ttnnijmegen/plantsensor/pcb/pdf/higrow1_etch_silk_bottom.pdf

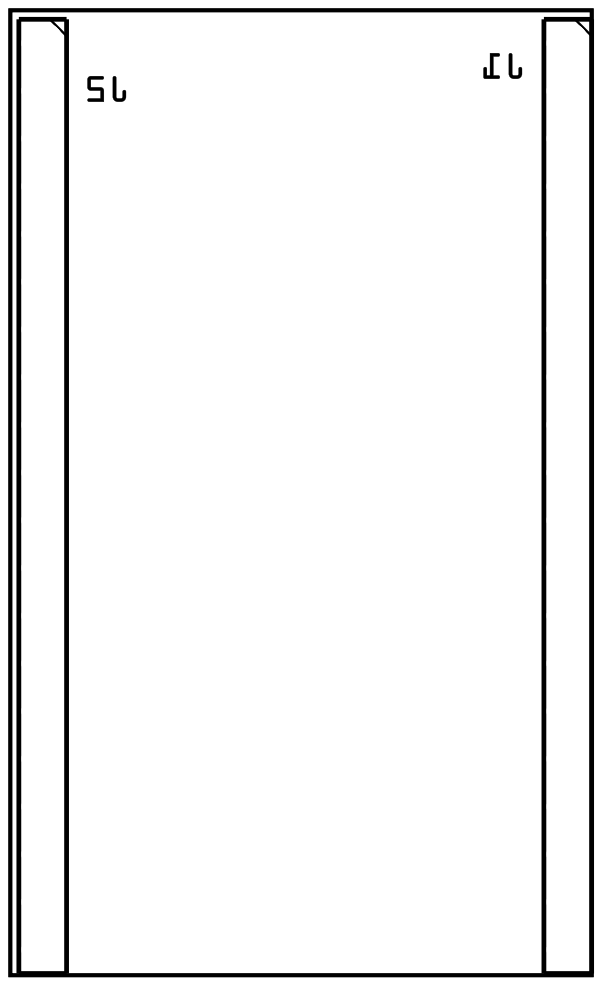
[picture p71: page 1]
