ttnnijmegen/plantsensor/pcb/pdf/higrow1_etch_silk_bottom_mirror.pdf

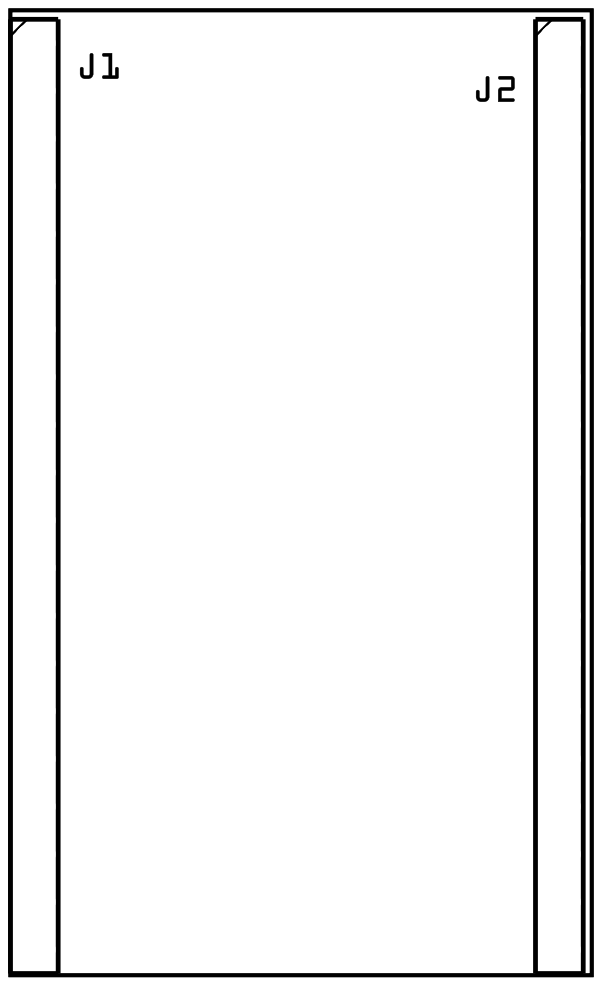
[picture p72: page 1]
