ttnnijmegen/plantsensor/pcb/pdf/higrow1_etch_silk_top.pdf

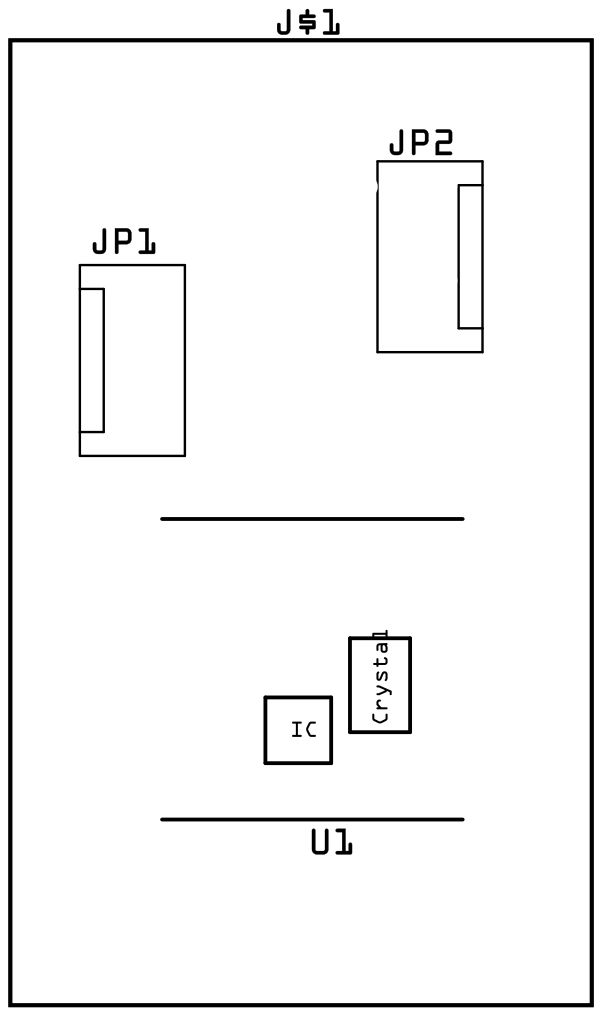
[picture p73: page 1]
