ttnnijmegen/plantsensor/pcb/pdf/higrow1_etch_silk_top_mirror.pdf

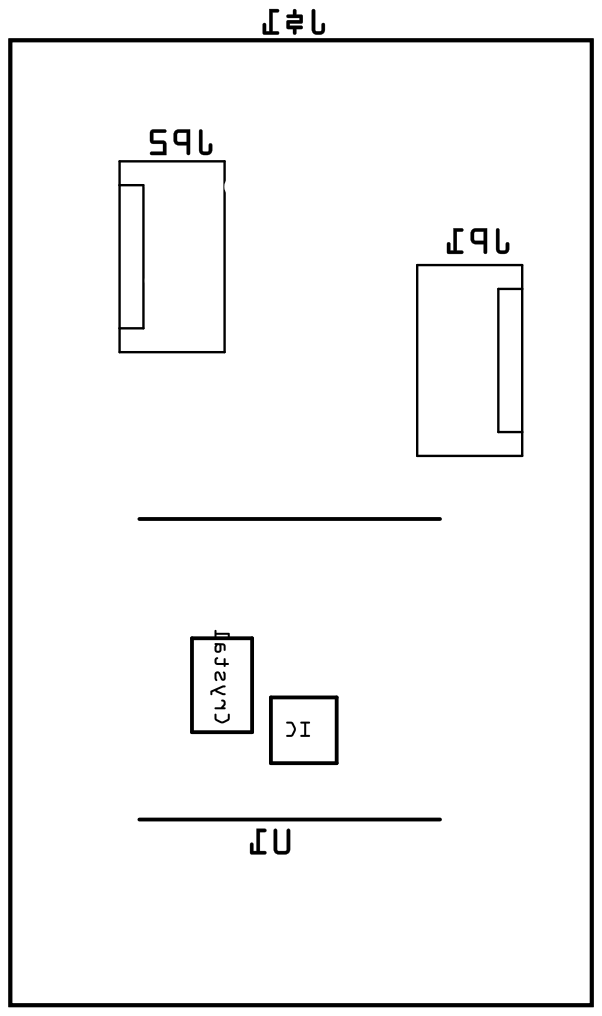
[picture p74: page 1]
